njhulsey/Jolt/Final_Photos/Board_Final_1.png

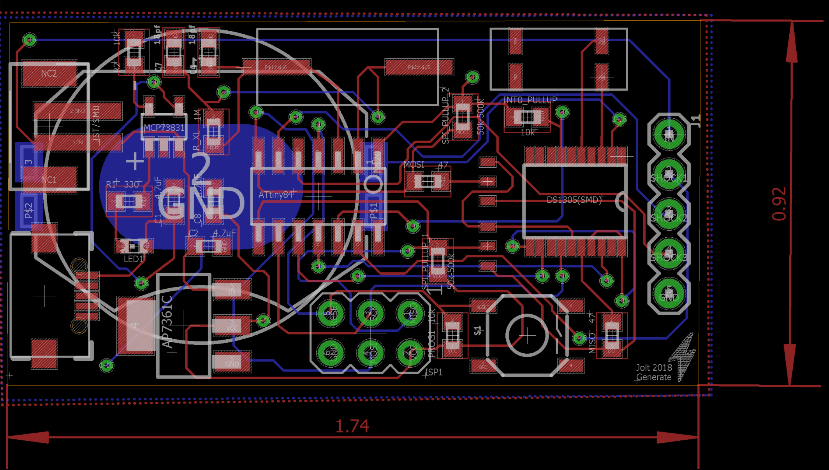
Final_Photos/Board_Final_1.png
