njhulsey/Jolt/Final_Photos/Display.jpg

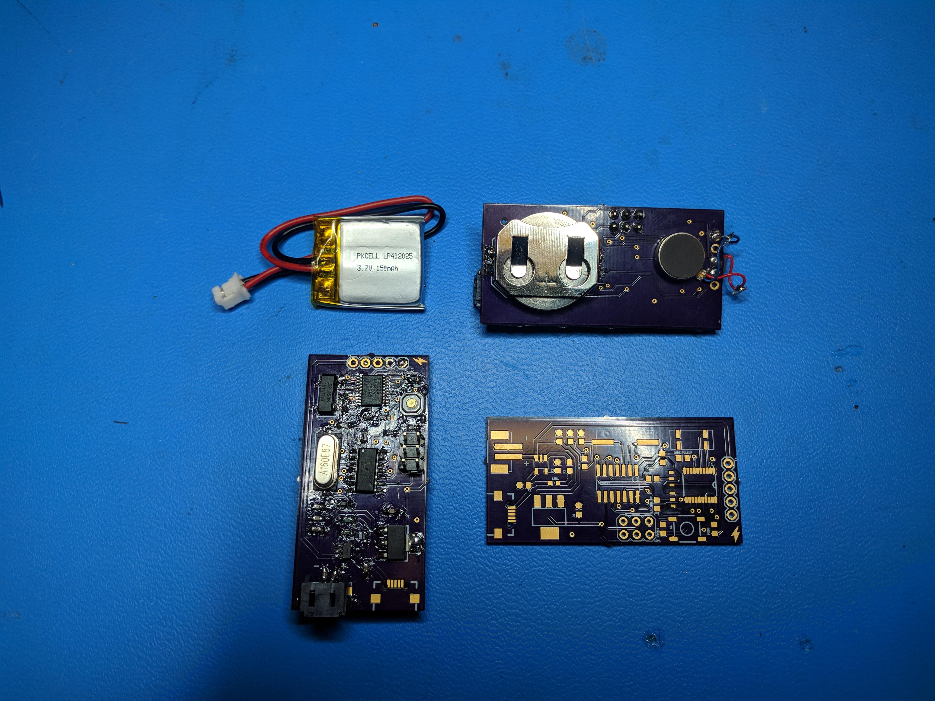
Final_Photos/Display.jpg
