njhulsey/Jolt/Final_Photos/Schematic_Final_1.png

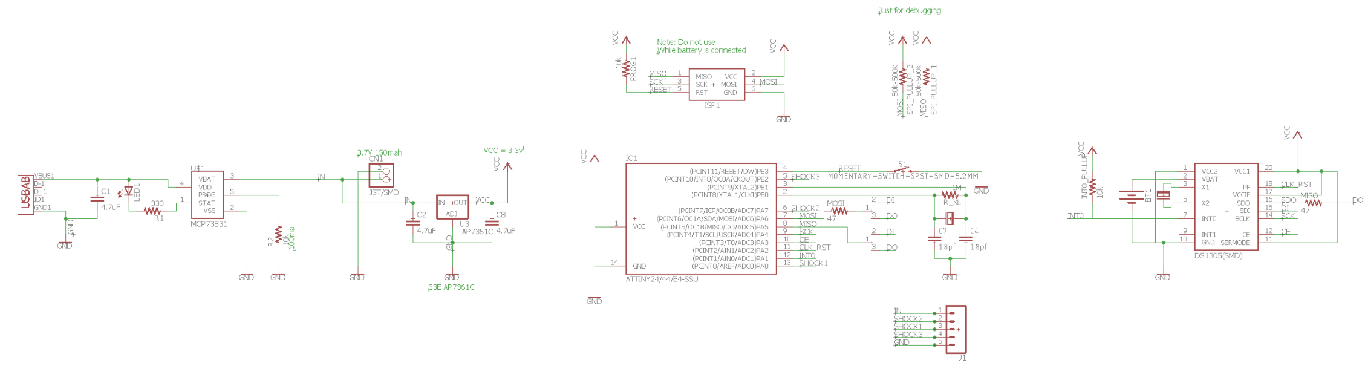
Final_Photos/Schematic_Final_1.png
