njhulsey/Jolt/Progress Photos/Board1.png

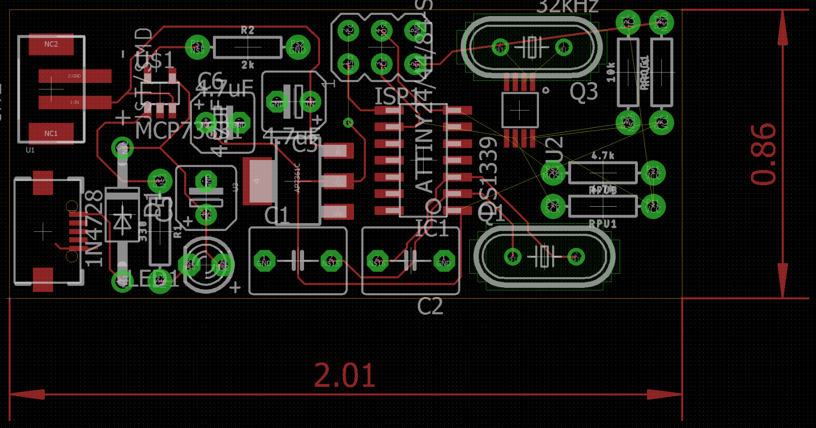
Progress Photos/Board1.png
