njhulsey/Jolt/Progress Photos/Board2.png

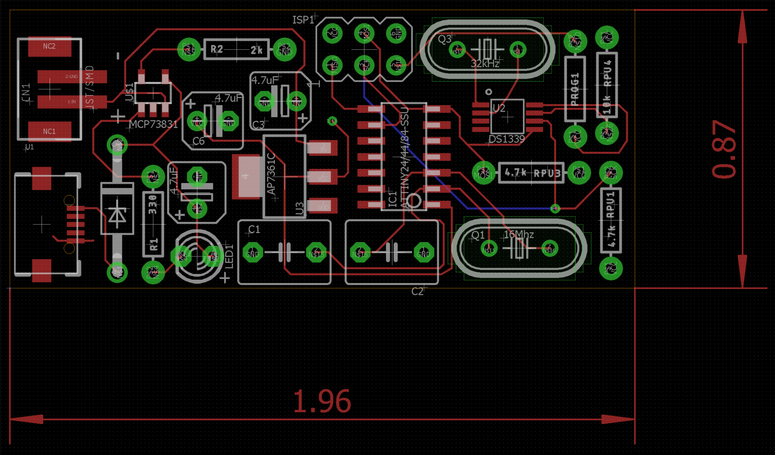
Progress Photos/Board2.png
