njhulsey/Jolt/Progress Photos/Board3.png

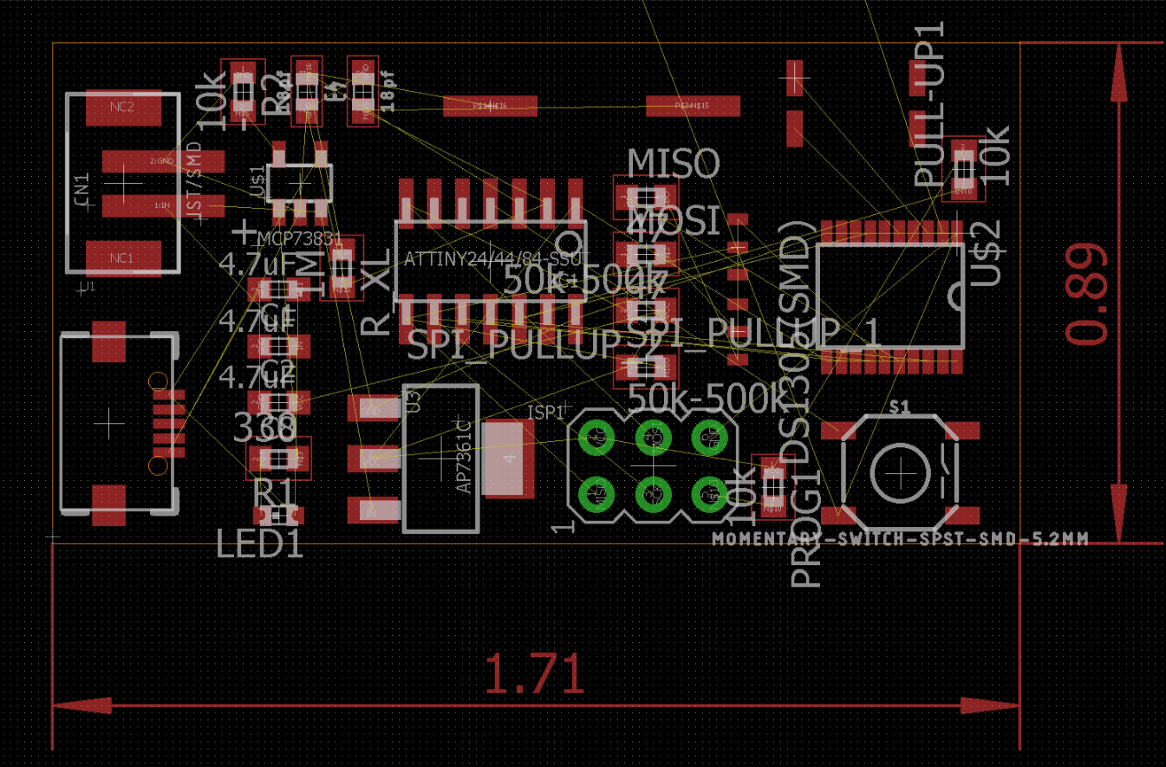
Progress Photos/Board3.png
