njhulsey/Jolt/Progress Photos/Board4.png

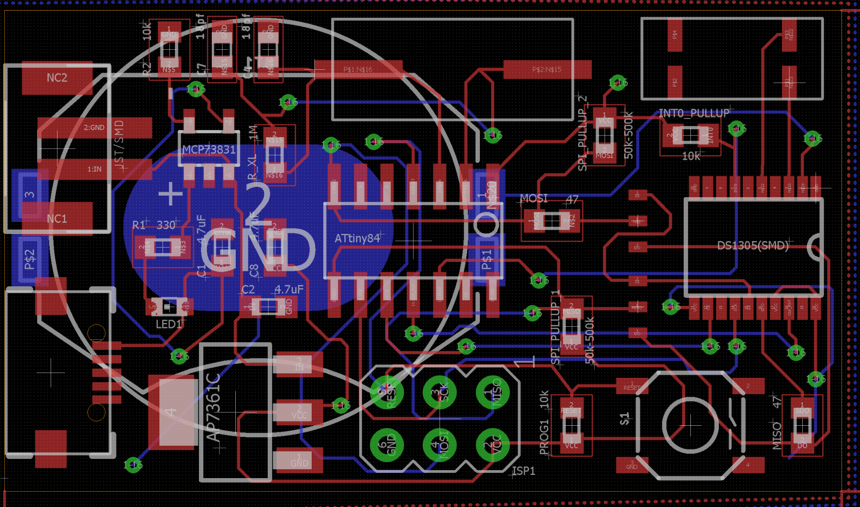
Progress Photos/Board4.png
