njhulsey/Jolt/Progress Photos/Board5.png

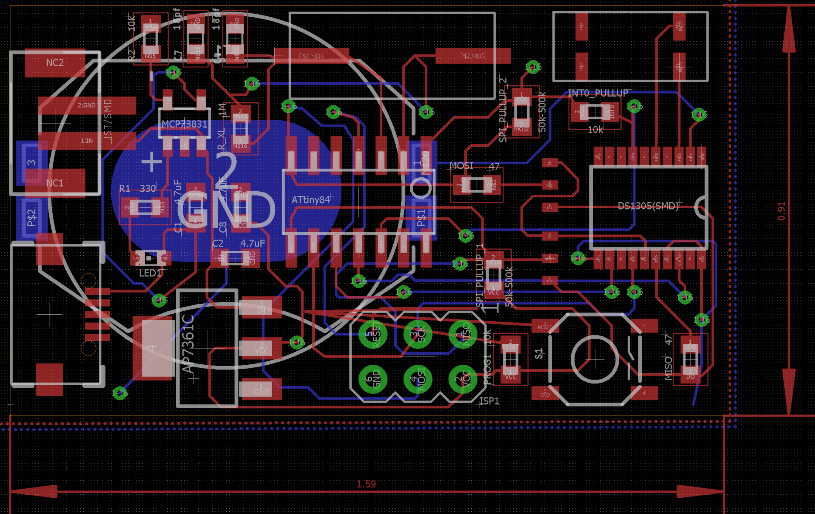
Progress Photos/Board5.png
