njhulsey/Jolt/Progress Photos/Board6.png

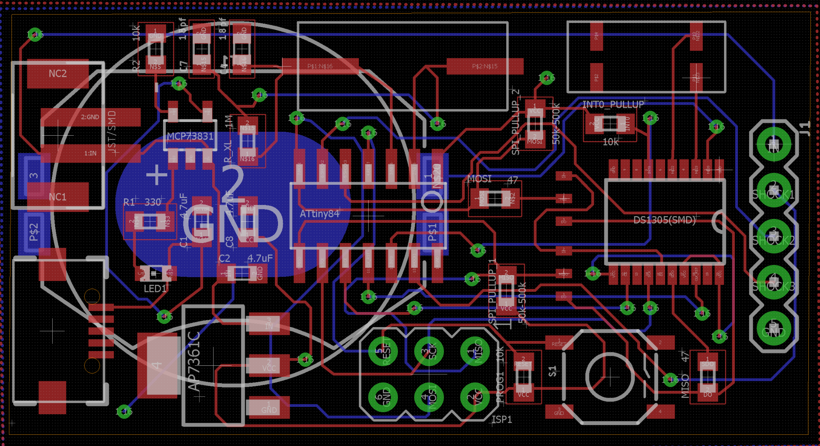
Progress Photos/Board6.png
