njhulsey/Jolt/Progress Photos/Final_Version1_Preview2.png

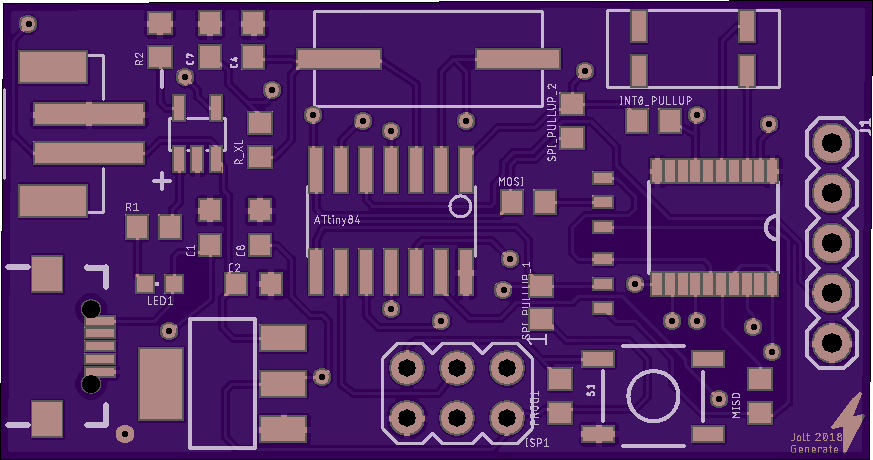
Progress Photos/Final_Version1_Preview2.png
