njhulsey/Jolt/Progress Photos/Final_Version1_Preview.png

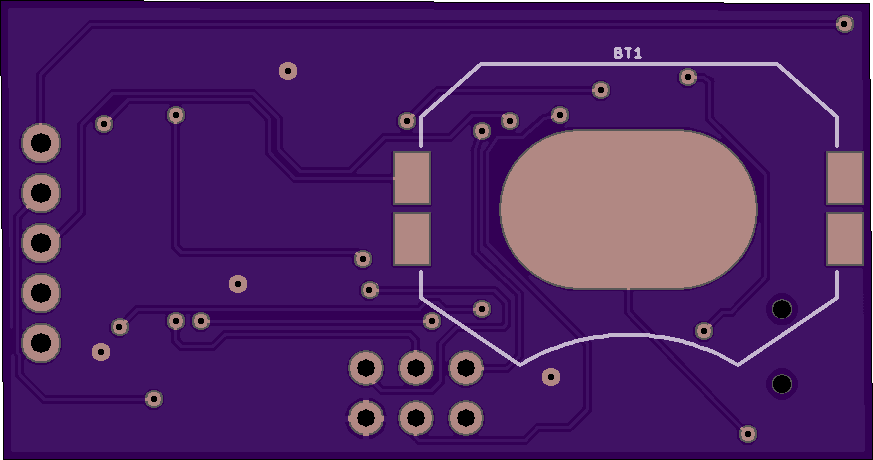
Progress Photos/Final_Version1_Preview.png
