njhulsey/Jolt/Progress Photos/Schematic3.png

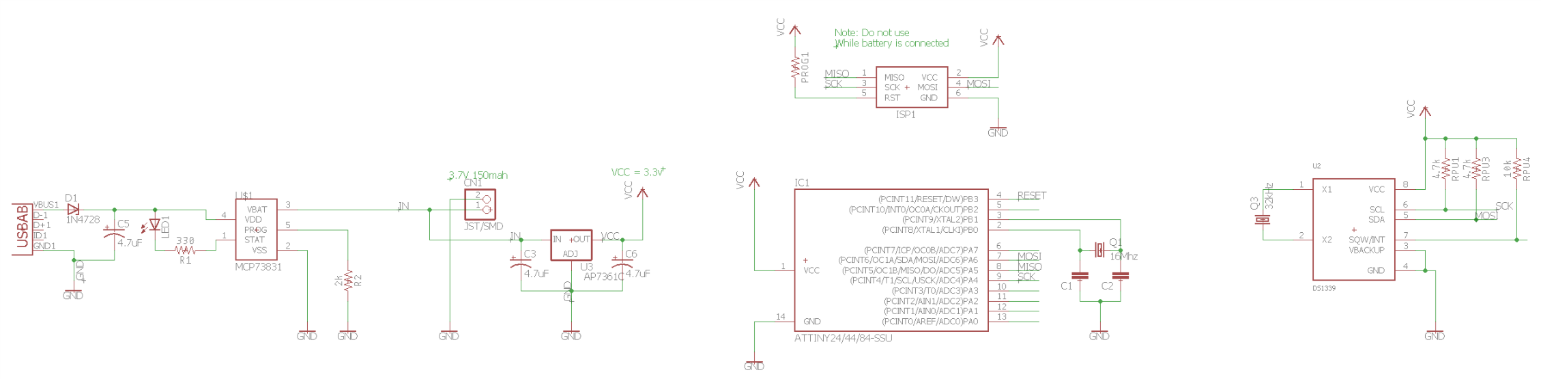
Progress Photos/Schematic3.png
