njhulsey/Jolt/Progress Photos/Schematic4.png

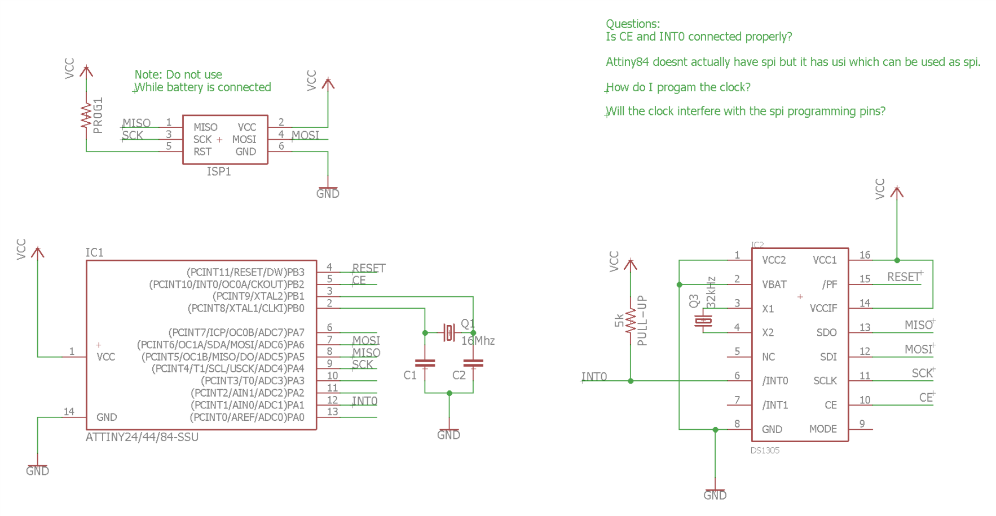
Progress Photos/Schematic4.png
